Squalius-cephalus/haili58/case/case_rev1/MX/Body.stl

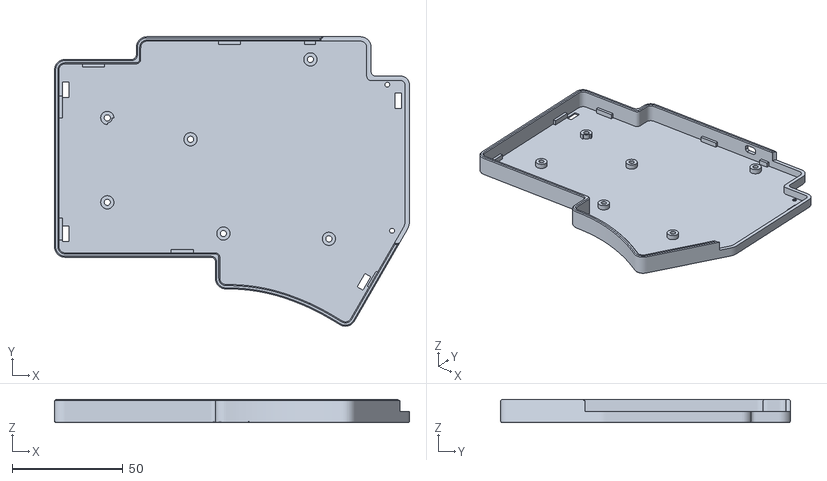
[picture p15: CAD file, 2026-01-26, an earlier design]
case/case_rev1/MX/Body.stl
160.2 x 130.7 x 10.4
