Squalius-cephalus/haili58/case/case_rev1/GLP/Plate.stl

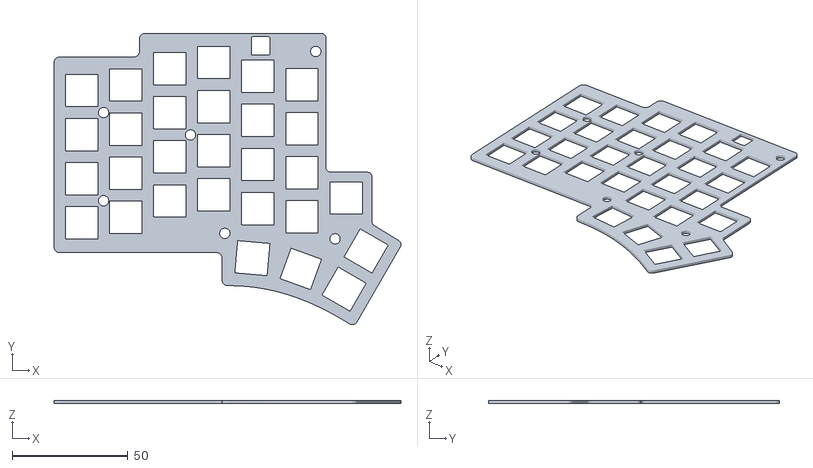
[picture p16: CAD file, 2026-01-25, an earlier design]
case/case_rev1/GLP/Plate.stl
149.9 x 125.9 x 1.40
